teehee567/Aevia/data/8776282029534908416-8776281726482505728-610848248425193474.png

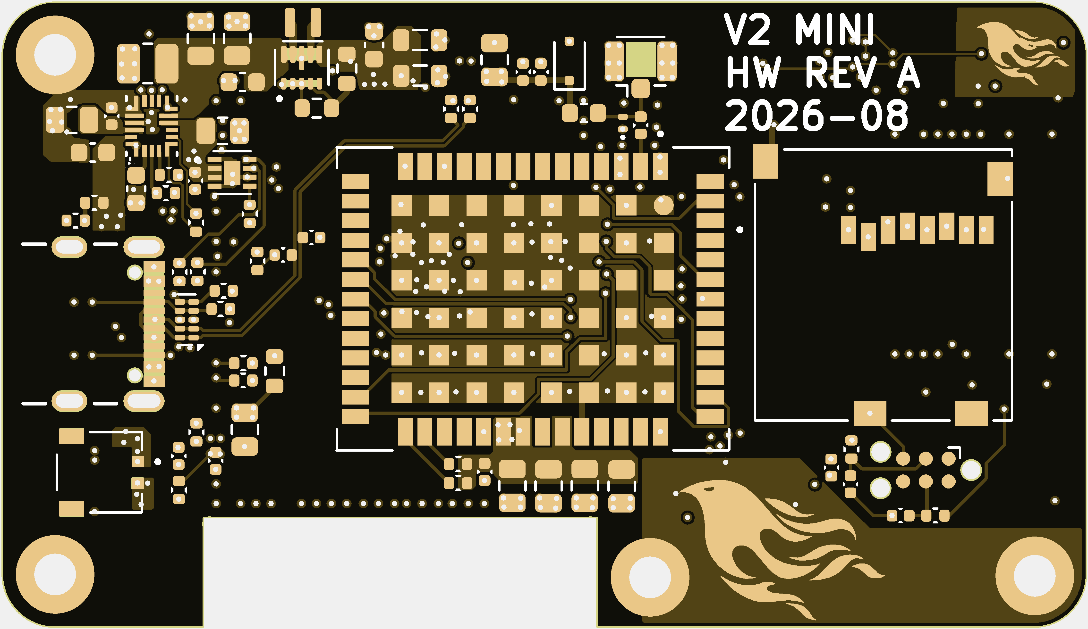
data/8776282029534908416-8776281726482505728-610848248425193474.png
